bigjosh/TSL-calibre-MSP/CCS Project/lcd_display.h

/*
 * lcd_display.h
 *
 *  Created on: Jan 20, 2023
 *      Author: passp
 */

#ifndef LCD_DISPLAY_H_
#define LCD_DISPLAY_H_

#include "util.h"

// *** LCD layout

extern "C" {

    constexpr word * LCDMEMW = (word *) LCDMEM;     // Word pointer to the LCD display memory

    constexpr byte LCDMEM_WORD_COUNT=16;             // Total number of words in LCD mem. Note that we do not actually use them all, but our display is spread across it.


    constexpr uint8_t DIGITPLACE_COUNT=12;

    // these arrays hold the pre-computed words that we will write to word in LCD memory that
    // controls the seconds and mins digits on the LCD. We keep these in RAM intentionally for power and latency savings.
    // use fill_lcd_words() to fill these arrays.

    #define SECS_PER_MIN 60

    #define MINS_PER_HOUR 60

    const byte READY_TO_LAUNCH_LCD_FRAME_COUNT=8;                             // How many frames in the ready-to-launch mode animation

    // Fills the arrays

    void initLCDPrecomputedWordArrays();


    void lcd_show_fast_secs( uint8_t secs );

    void lcd_show_digit_f( const uint8_t pos, const byte d );

    void lcd_show_testing_only_message();

    // Show "tEStIng"
    void lcd_show_testing_message();

    // For now, show all 9's.
    // TODO: Figure out something better here

    void lcd_show_long_now();


    // Squigle segments are used during the Ready To Launch mode animation before the pin is pulled
    constexpr unsigned SQUIGGLE_ANIMATION_FRAME_COUNT = 8;          // There really should be a better way to do this.

    // Show a frame n the ready-to-lanuch squiggle animation
    // 0 <= step < SQUIGGLE_ANIMATION_FRAME_COUNT

    void lcd_show_squiggle_frame( byte step );


    // Fill the screen with horizontal dashes
    void lcd_show_dashes();

    // Fill the screen with X's
    void lcd_show_XXX();

    void lcd_show_load_pin_message();

    constexpr unsigned LOAD_PIN_ANIMATION_FRAME_COUNT = 5;      // Dash sliding to the right to point ot the trigger pin
    void lcd_show_load_pin_animation(unsigned int step);

    // The lance is 2 digitplaces wide so we need extra frames to show it coming onto and off of the screen
    constexpr unsigned LANCE_ANIMATION_FRAME_COUNT = DIGITPLACE_COUNT+3;          // There really should be a better way to do this.

    // Show "First Start"
    void lcd_show_first_start_message();

    // Show the message "Error cOde X" on the lcd.
    void lcd_show_errorcode( byte code  );

    // Show the message "bAtt Error X" on the lcd.
    void lcd_show_batt_errorcode( byte code  );

    // Show "Pin iS Pin"
    void lcd_show_pin_in_err_message();

    // Show "-Arming-"
    void lcd_show_arming_message();

    // Show "CLOCK GOOd"
    void lcd_show_clock_good_message();

    // Show "CLOCK LOSt"
    void lcd_show_clock_lost_message();

    // Every 100 days
    void lcd_show_centesimus_dies_message();

    // Fill the screen with 0's
    void lcd_show_zeros();

    // Show "888888888888"
    void lcd_show_all_8s_message();

    void lcd_show_amps_hi_message( unsigned count );

    void lcd_show_amps_lo_message( unsigned count );

    void lcd_show_lo_volt_message( unsigned count );



    // these arrays hold the pre-computed words that we will write to word in LCD memory that
    // controls the seconds and mins digits on the LCD. We keep these in RAM intentionally for power and latency savings.
    // use fill_lcd_words() to fill these arrays.

    extern word secs_lcd_words[SECS_PER_MIN];

    // Write a value from this array into this word to update the two digits on the LCD display
    extern word *secs_lcdmem_word;

    struct lcd_save_screen_buffer_t {
        unsigned w[LCDMEM_WORD_COUNT];
    };


    // Save the current LCD display pixels
    void lcd_save_screen( lcd_save_screen_buffer_t *buffer);

    // Restore the current LCD display pixels
    void lcd_restore_screen( lcd_save_screen_buffer_t *buffer);

}

#endif /* LCD_DISPLAY_H_ */


// Show the digit x at position p
// where p=0 is the rightmost digit

template <uint8_t pos, uint8_t x>                    // Use template to force everything to compile down to an individualized, optimized function for each pos+x combination
inline void lcd_show();
// Show the digit x at position p
// where p=0 is the rightmost digit
