bigjosh/TSL-calibre-MSP/CCS Project/util.h

/*
 * util.h
 *
 * Some handy stuffs
 *
 *  Created on: Oct 15, 2022
 *      Author: passp
 */

#ifndef UTIL_H_
#define UTIL_H_


#define _BV(x) (1<<(x))               // bit value (Thanks Claude!)

#define SBI(x,b) ((x) |= _BV(b))       // set bit b in x
#define CBI(x,b) ((x) &= ~_BV(b))      // clear bit b in x
#define TBI(x,b) (((x) & _BV(b))!=0)   // test bit b in x

typedef unsigned char uint8_t;
typedef unsigned int  uint16_t;
typedef unsigned long uint32_t;

typedef unsigned char byte;
typedef unsigned int  word;

#endif /* UTIL_H_ */
